brainsmoke/psu_case/scad/cover_hole_test.scad

use <cover.scad>

print_orientation()
color("red")
intersection()
{
	translate([-17.,-40,20])
	cube([10, 30, 10]);
	cover();
}
